richimoeller/Balancing-Cube-ESP32-based-on-REMRC-s-work/esp32_cube_enc_rot/ESP32.h

#define BUZZER      27
#define VBAT        34
#define INT_LED     2

#define BRAKE       26

#define DIR2        15
#define ENC2_1      13
#define ENC2_2      14
#define PWM2        25
#define PWM2_CH     0

#define DIR3        5
#define ENC3_1      16
#define ENC3_2      17
#define PWM3        18
#define PWM3_CH     2

#define DIR1        4
#define ENC1_1      35
#define ENC1_2      33
#define PWM1        32
#define PWM1_CH     1

#define TIMER_BIT   8
#define BASE_FREQ   20000

#define MPU6050       0x68   // Device address
#define ACCEL_CONFIG  0x1C   // Accelerometer configuration address
#define GYRO_CONFIG   0x1B   // Gyro configuration address
#define PWR_MGMT_1    0x6B
#define PWR_MGMT_2    0x6C

#define accSens 0            // 0 = 2g, 1 = 4g, 2 = 8g, 3 = 16g
#define gyroSens 0           // 0 = 250rad/s, 1 = 500rad/s, 2 1000rad/s, 3 = 2000rad/s

#define EEPROM_SIZE   64

#define LED_PIN       19     // Pin that connects to WS2812B
#define NUM_PIXELS    3      // The number of LEDs (pixels) on WS2812B

float Gyro_amount = 0.996;

bool vertical_vertex = false;
bool vertical_edge = false;
bool calibrating = false;
bool vertex_calibrated = false;
bool calibrated = false;
bool calibrated_leds = false;
// new variable (by rmo)
bool rotating = false;
//bool rotating_positive = false;
//bool rotating_negative = false;

float K1 = 180;
float K2 = 30.00; 
float K3 = 1.6;
float K4 = 0.008;
float zK2 = 8.00;
float zK3 = 0.30;

float eK1 = 190;
float eK2 = 31.00; 
float eK3 = 2.5;
float eK4 = 0.014;

int loop_time = 15;

struct OffsetsObj {
  int ID;
  float acXv;
  float acYv;
  float acZv;
  float acXe;
  float acYe;
  float acZe;
};
OffsetsObj offsets;

float alpha = 0.7;

int16_t  AcX, AcY, AcZ, AcXc, AcYc, AcZc, GyX, GyY, GyZ;
float gyroX, gyroY, gyroZ, gyroXfilt, gyroYfilt, gyroZfilt;
float speed_X, speed_Y;

// new variable (by rmo)
int16_t  pwm_offset = 0;
//int16_t  pos_pwm_offset = 70;
//int16_t  neg_pwm_offset = -70;
//int      ramp_up_divider = 3; 

int16_t  GyZ_offset = 0;
int16_t  GyY_offset = 0;
int16_t  GyX_offset = 0;
int32_t  GyZ_offset_sum = 0;
int32_t  GyY_offset_sum = 0;
int32_t  GyX_offset_sum = 0;

float robot_angleX, robot_angleY;
float Acc_angleX, Acc_angleY;      
int32_t motors_speed_X; 
int32_t motors_speed_Y;
int32_t motors_speed_Z;   

long currentT, previousT_1, previousT_2;

volatile int  enc_count1 = 0, enc_count2 = 0, enc_count3 = 0;
int16_t motor1_speed;         
int16_t motor2_speed;         
int16_t motor3_speed;     
